hemidactylus/opabinia/app/mockMeasurer.py

#!/usr/bin/python3

'''
    Generation of mock passage data for testing
'''
from __future__ import print_function

from time import sleep
from datetime import datetime
from random import random
import sys

from dboperations import (
    checkAndOpenDatabase,
    dbOpenDatabase,
    dbSaveRow,
)
from config import (
    dbName
)

minTime=12
maxTime=36

if __name__=='__main__':

    db=checkAndOpenDatabase(dbName)
    print('Init mock measurer.')
    while True:
        tVal=-1 if random()<0.5 else +1
        print('* %s *' % datetime.now().strftime('%H:%M:%S'))
        sys.stdout.flush()
        dbSaveRow(db,{'count':tVal,'abscount':abs(tVal)})
        db.commit()
        sleep(random()*(maxTime-minTime)+minTime)
