hemidactylus/opabinia/app/dateutils.py

'''
    dateutils.py : various date manipulation
    (including timezone hell)
'''

import pytz
from datetime import datetime, timedelta, date
import time

from config import (
    timeZone,
    dateFormat,
    niceDateFormat,
    maxNumCounterEntries,
)

monthNames=[
    'January',
    'February',
    'March',
    'April',
    'May',
    'June',
    'July',
    'August',
    'September',
    'October',
    'November',
    'December',
]

def findPreviousMidnight(naiveDT):
    '''
        given a naive date, returns the utc date
        of the most recent midnight (for that timezone,
        but recast as utc)

        Somehow this seems to work, but damn timezones!
    '''
    locMidnight = pytz \
        .timezone(timeZone) \
        .localize(datetime(*localiseDate(naiveDT).timetuple()[:3]))
    return datetime(*locMidnight.utctimetuple()[:5])

def localiseDate(dt):
    locDate=pytz.utc.localize(dt,is_dst=None)
    return locDate.astimezone(pytz.timezone(timeZone))

def javaTimestamp(pDate):
    return time.mktime(pDate.timetuple())*1000.0

def localiseRow(row):
    nrow={k:v for k,v in row.items()}
    if nrow['time'] is not None:
        nrow['time']=localiseDate(row['time'])
        nrow['jtimestamp']=javaTimestamp(nrow['time'])
    return nrow

def timeBounds(datename):
    '''
        given a datename, i.e.
            '2017-03-23'
        or
            'today', 'yesterday'
        two things are returned:
        the date and the previous midnight, both
        as utc datetimes
    '''
    if datename=='today':
        reqDate=datetime(*localiseDate(datetime.utcnow()).date().timetuple()[:3])
    elif datename=='yesterday':
        reqDate=datetime(*localiseDate(datetime.utcnow()-timedelta(days=1)).date().timetuple()[:3])
    else:
        try:
            reqDate=datetime.strptime(datename,dateFormat)
        except:
            reqDate=datetime.utcnow()
    lastMidnight=findPreviousMidnight(reqDate)
    return reqDate,lastMidnight

def normaliseReqDate(rdate):
    '''
        when possible brings the date string
        to a name, for setting the active buttons
        in the web page
    '''
    for possibleName in ['today','yesterday']:
        if rdate==possibleName or timeBounds(possibleName)[0].strftime(dateFormat)==rdate:
          return possibleName
    return rdate

def sortAndLocalise(evtList,maxItems=maxNumCounterEntries):
    '''
        this also reduces, if necessary, the number of entries.
        Pass maxItems = None to suppress this behaviour
    '''
    fullList=sorted(
        (
            localiseRow(evt)
            for evt in evtList
        ),
        key=lambda evt: evt['time'],
        reverse=True,
    )
    # OPTION 1 is to limit the returned to the LAST items
    # if maxItems is not None:
    #     finalList=fullList[:maxItems]
    # else:
    #     finalList=fullList
    # OPTION 2 is to carefully remove the shortest-lived entries
    # (but the most recent, i.e. element zero, always survives!)
    if maxItems is not None and len(fullList)>maxItems:
        # find the span threshold
        spanThreshold=sorted(
            (
                (e2['time']-e1['time']).total_seconds()
                for e1,e2 in zip(fullList[1:-1],fullList[2:])
            ),
            reverse=True,
        )[maxItems-1]
        finalList=[fullList[0]]+[
            e1
            for e1,e2 in zip(fullList[1:-1],fullList[2:])
            if (e2['time']-e1['time']).total_seconds() > spanThreshold
        ]
    else:
        finalList=fullList
    #
    return finalList

def roundTime(dt, roundToSeconds):
   """
           Round a datetime object to any time laps in seconds
           dt : datetime.datetime object, default now.
           roundTo : Closest number of seconds to round to, default 1 minute.
           Author: Thierry Husson 2012 - Use it as you want but don't blame me.

            h/t "Le Droid" from https://stackoverflow.com/questions/3463930/
                                how-to-round-the-minute-of-a-datetime-object-python

   """
   seconds = (dt.replace(tzinfo=None) - dt.min).seconds
   rounding = (seconds+roundToSeconds/2) // roundToSeconds * roundToSeconds
   return dt + timedelta(0,rounding-seconds,-dt.microsecond)

def timeHistogram(evtList,barSeconds):
    '''
        given a list of events with time and count=+/-1,
        a histogram of pairs of values is prepared
        along time, with a given quantisation
    '''
    if len(evtList)==0:
        return []
    else:
        maxTime=roundTime(
            max(ev['time'] for ev in evtList),
            barSeconds,
        )
        minTime=roundTime(
            min(ev['time'] for ev in evtList),
            barSeconds,
        )
        numDates=int((maxTime-minTime).total_seconds()/barSeconds)
        allDates=[
            minTime+timedelta(seconds=i*barSeconds)
            for i in range(numDates+1)
        ]
        histo={
            tDate : {
                'time': tDate,
                'jtimestamp': javaTimestamp(tDate),
                'ins': 0,
                'outs': 0,
                'nets': 0,
                'span': 1000.0*barSeconds,
            }
            for tDate in allDates
        }
        for evt in evtList:
            qDate=roundTime(evt['time'],barSeconds)
            if evt['count']>0:
                histo[qDate]['ins']+=1
            elif evt['count']<0:
                histo[qDate]['outs']+=1
        for hItem in histo.values():
            hItem['nets']=hItem['ins']-hItem['outs']
        return sorted(
            histo.values(),
            key=lambda hData: hData['time'],
            reverse=True,
        )
